shadylanebees/3FrameMatingNuc/20161227_194710.jpg

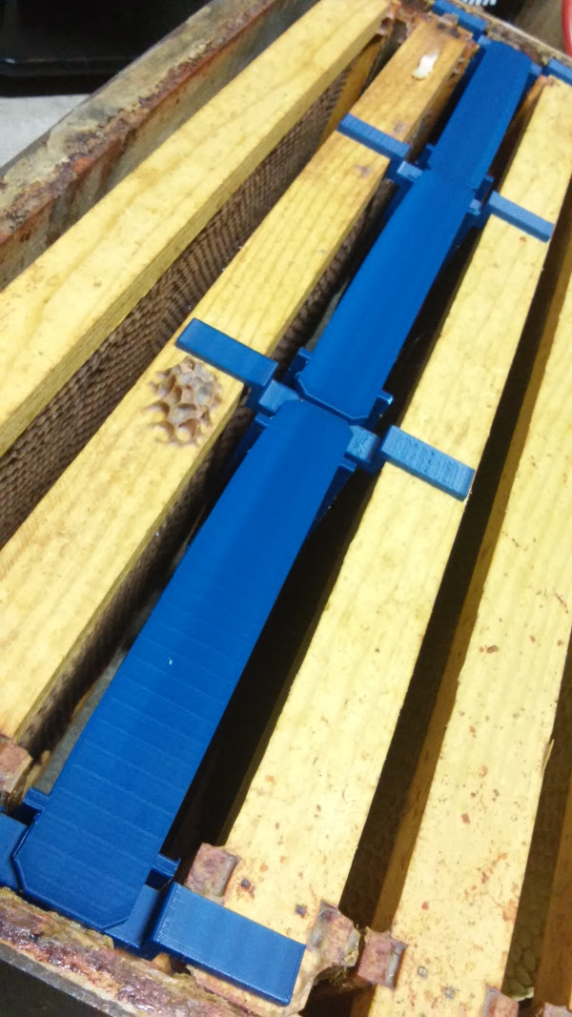
20161227_194710.jpg
